nghiado06/balancing-robot-esp32/balancing-robot-firmware/include/pins.h

#ifndef PINS_H
#define PINS_H

/****************************************************************************************************
 * =========================================== [ BUTTON ] ===========================================
 ***************************************************************************************************/
#define BUTTON_CALIB_PIN 36
#define BUTTON_MODE_PIN 39
#define BUTTON_ARM_PIN 34

/****************************************************************************************************
 * =========================================== [ BUZZER ] ===========================================
 ***************************************************************************************************/
#define BUZZER_PIN 32
#define LEDC_CH_BUZZER 2

/****************************************************************************************************
 * =========================================== [ MPU6050 ] ==========================================
 ***************************************************************************************************/
#define SDA_PIN 21
#define SCL_PIN 22

/****************************************************************************************************
 * =========================================== [ HC-SR04 ] ==========================================
 ***************************************************************************************************/
#define TRIG_PIN 17
#define ECHO_PIN 19

/****************************************************************************************************
 * ========================================== [ STEPPER 1 ] =========================================
 ***************************************************************************************************/
#define DIR_L_PIN 27
#define STEP_L_PIN 14
#define ENABLE_PIN 16

/****************************************************************************************************
 * ========================================== [ STEPPER 2 ] =========================================
 ***************************************************************************************************/
#define DIR_R_PIN 33
#define STEP_R_PIN 25

/****************************************************************************************************
 * =========================================-= [ MAX7219 ] ==========================================
 ***************************************************************************************************/
#define DIN_PIN 23
#define SCLK_PIN 18
#define CS_PIN 5

#endif // PINS_H
